mon/PocketVoltex/Software/WebConfig/img/r6-topdown-small.png

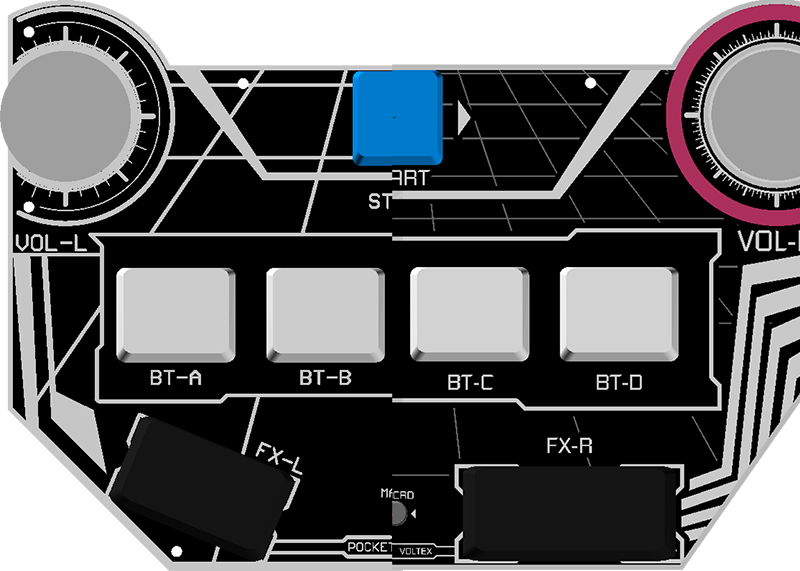
Software/WebConfig/img/r6-topdown-small.png
